TomahawkLabsKB/m3501_stm32f072/Firmware/Locking Switch Logic/Keymap_C_Explanation1.png

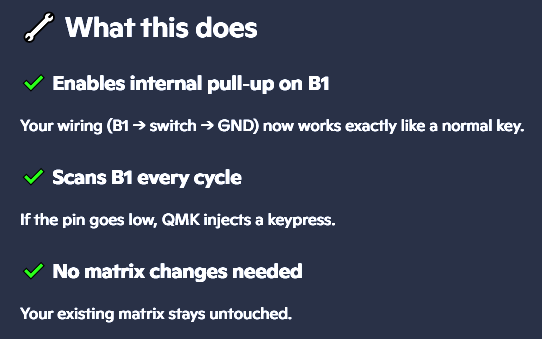
Firmware/Locking Switch Logic/Keymap_C_Explanation1.png
