TomahawkLabsKB/m3501_stm32f072/Firmware/Locking Switch Logic/Keymap_C_Explanation2.png

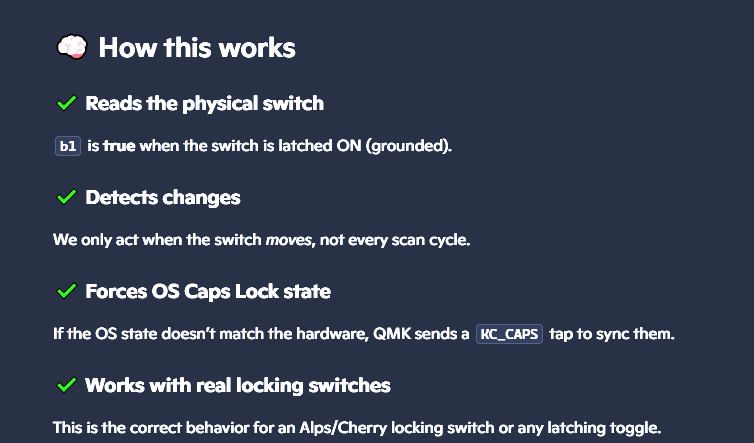
Firmware/Locking Switch Logic/Keymap_C_Explanation2.png
