TomahawkLabsKB/m3501_stm32f072/Images/Cable/Oops.jpeg

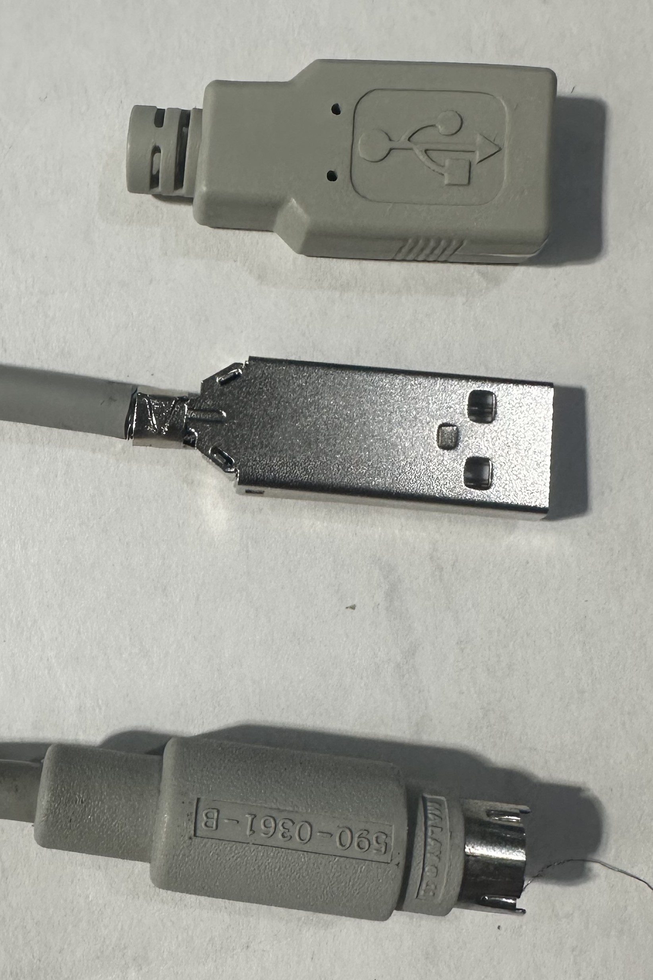
Images/Cable/Oops.jpeg
