TomahawkLabsKB/m3501_stm32f072/Images/Cable/SheathingLength.jpeg

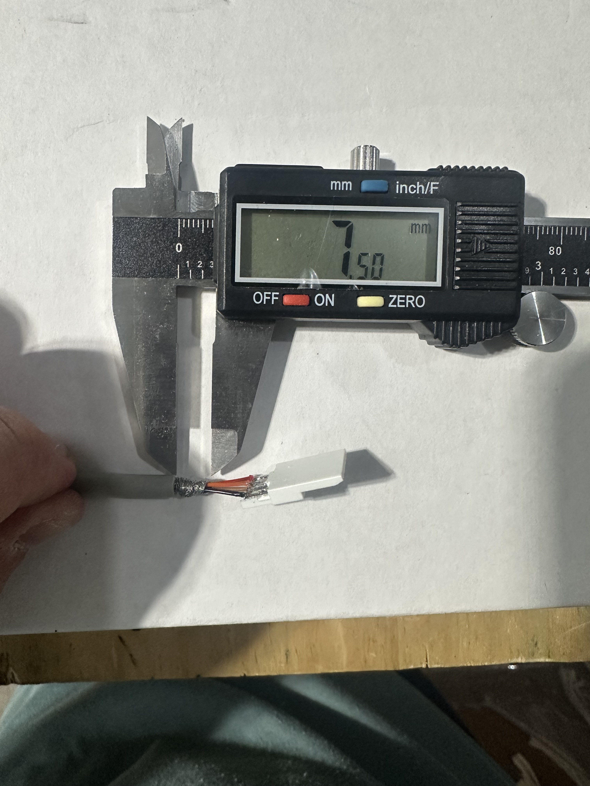
Images/Cable/SheathingLength.jpeg
