TomahawkLabsKB/m3501_stm32f072/Images/Cable/WireLength.jpeg

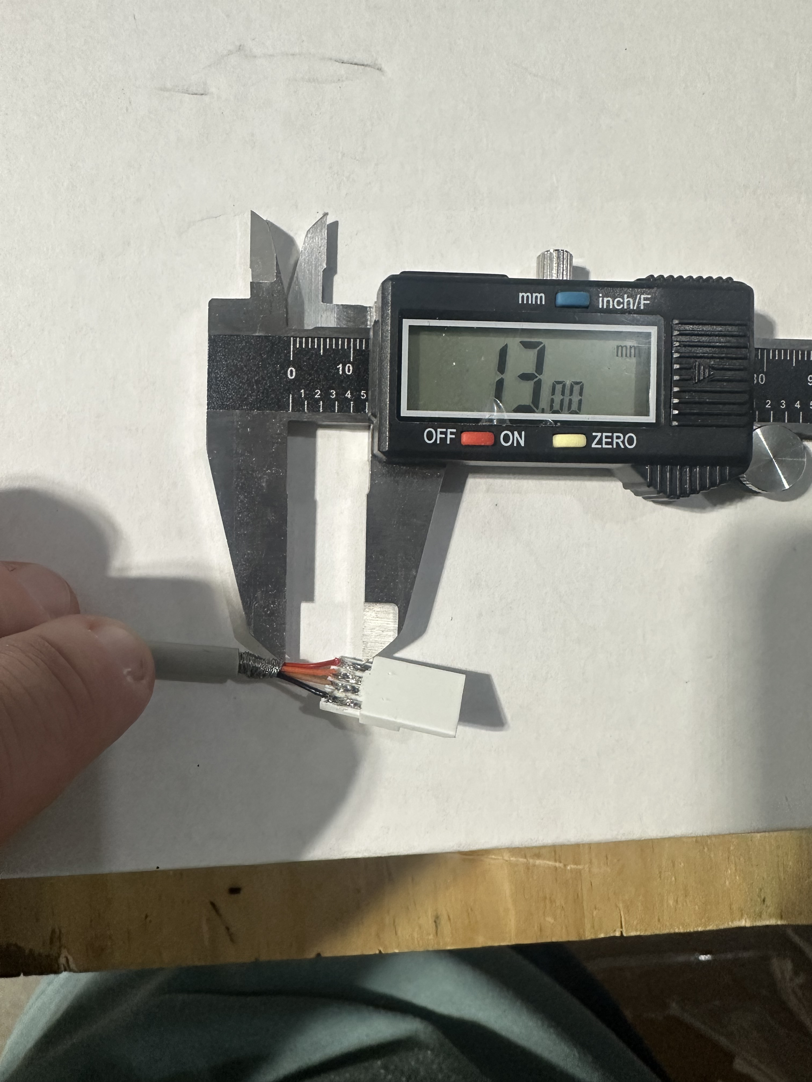
Images/Cable/WireLength.jpeg
