TomahawkLabsKB/m3501_stm32f072/Images/Daughterboard/Daughterboard.jpeg

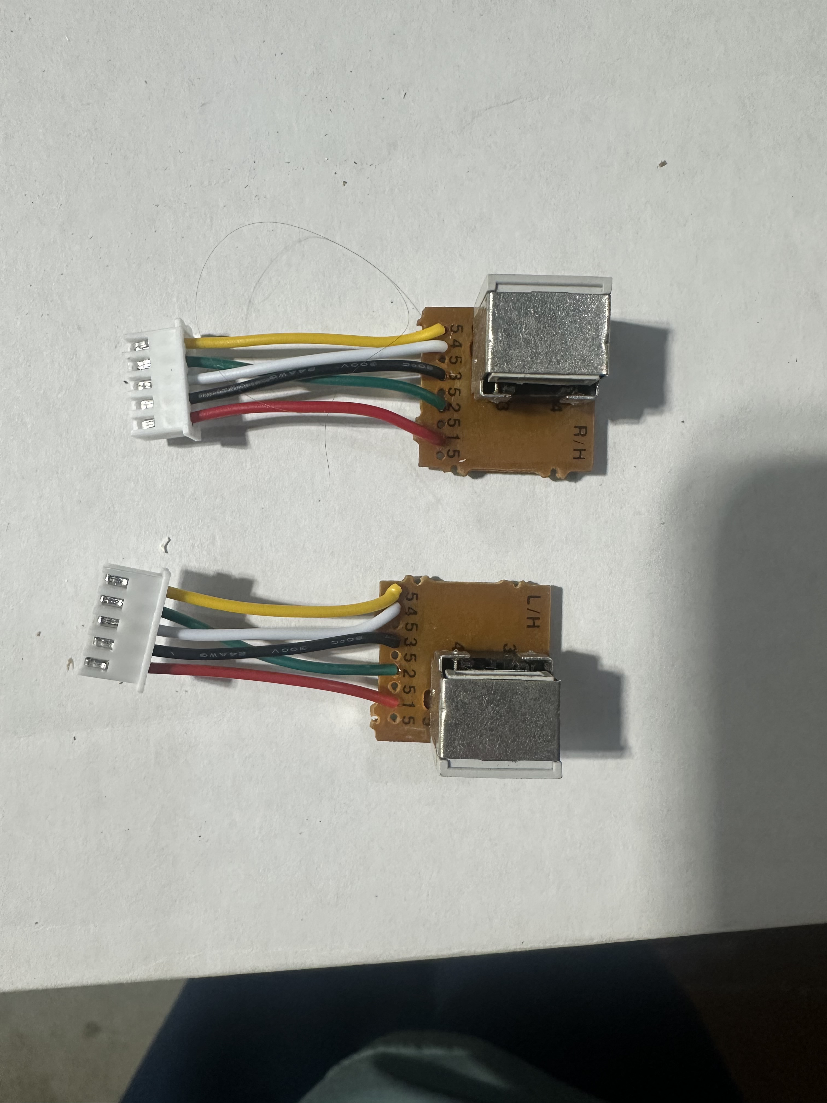
Images/Daughterboard/Daughterboard.jpeg
