TomahawkLabsKB/m3501_stm32f072/Images/Daughterboard/DaughterboardLength.jpeg

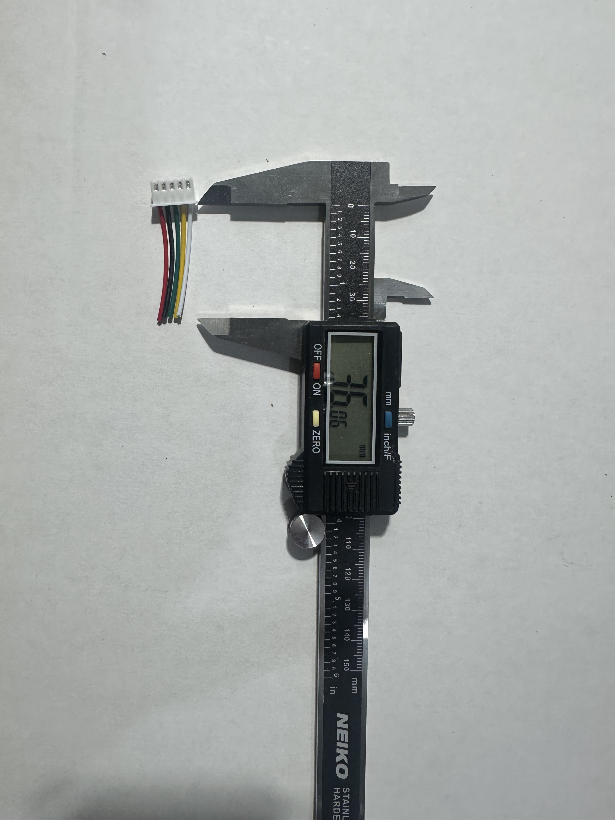
Images/Daughterboard/DaughterboardLength.jpeg
