TomahawkLabsKB/m3501_stm32f072/Images/Daughterboard/LeftDaughterboard.jpeg

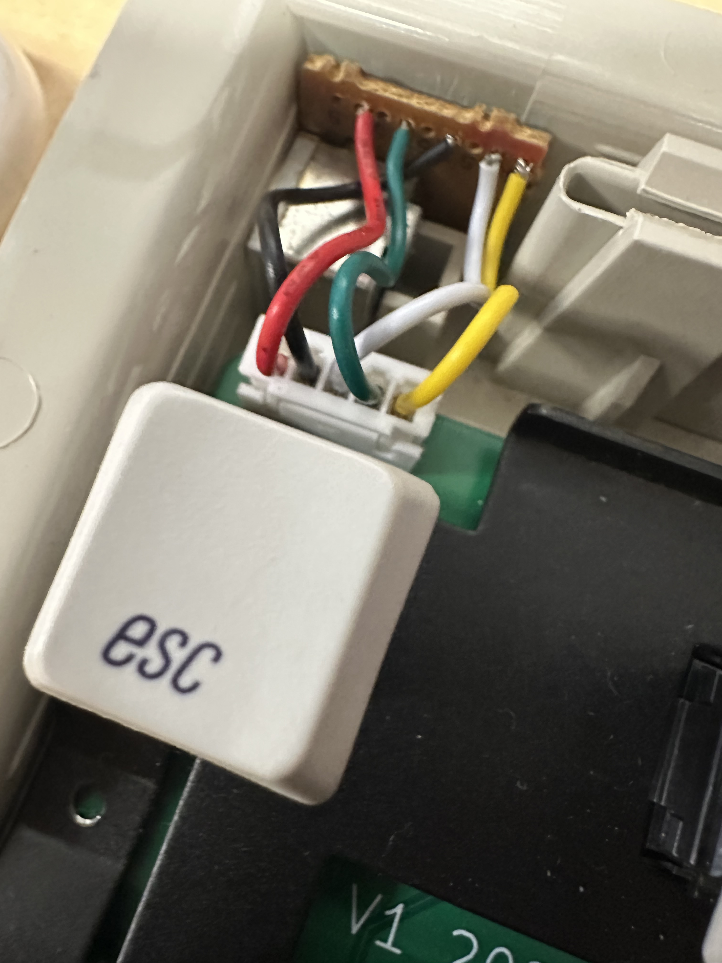
Images/Daughterboard/LeftDaughterboard.jpeg
