TomahawkLabsKB/m3501_stm32f072/Images/Daughterboard/RightDaughterboard.jpeg

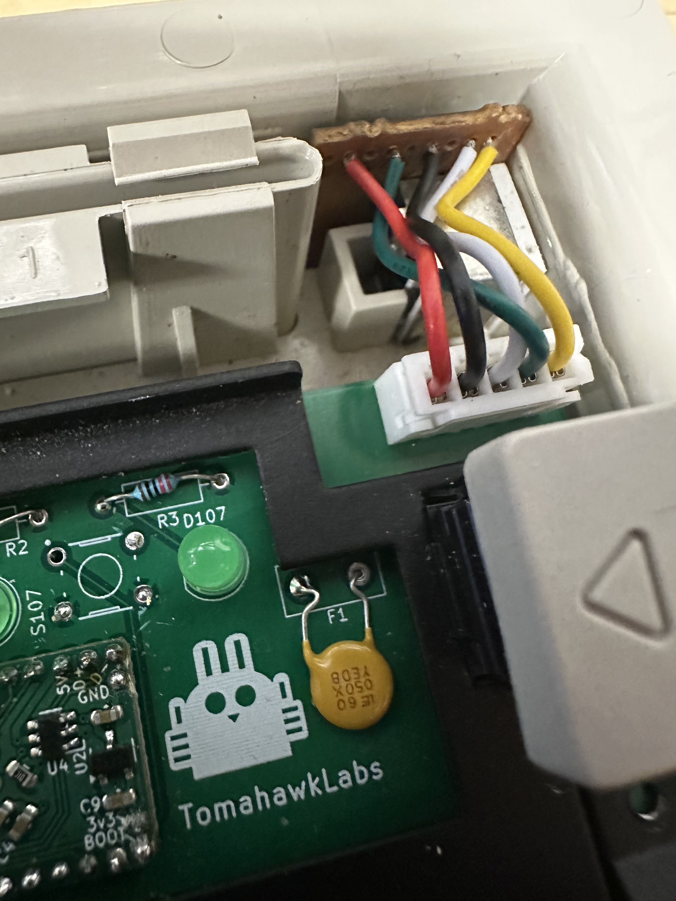
Images/Daughterboard/RightDaughterboard.jpeg
