TomahawkLabsKB/m3501_stm32f072/Images/PCB/Diodes.jpeg

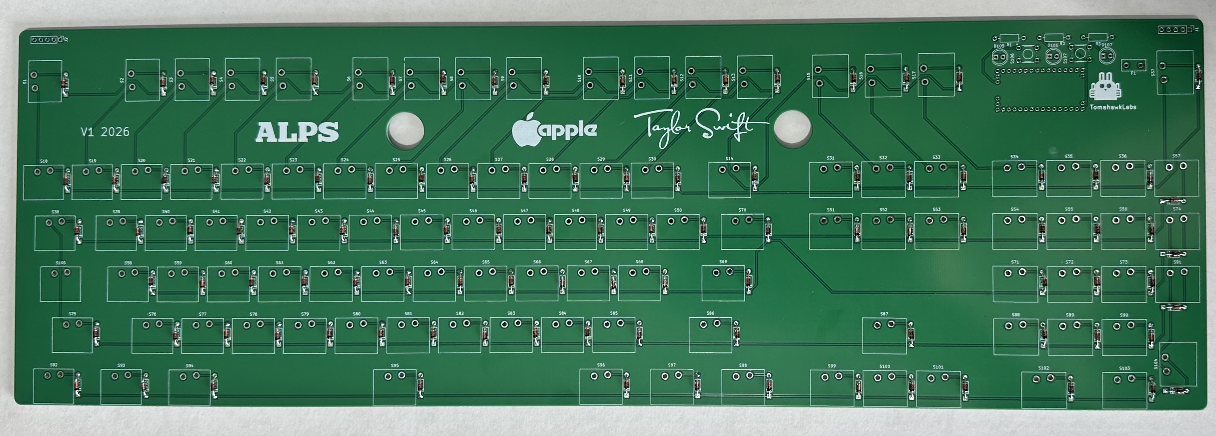
Images/PCB/Diodes.jpeg
