TomahawkLabsKB/m3501_stm32f072/Images/PCB/FullyPopulated.jpeg

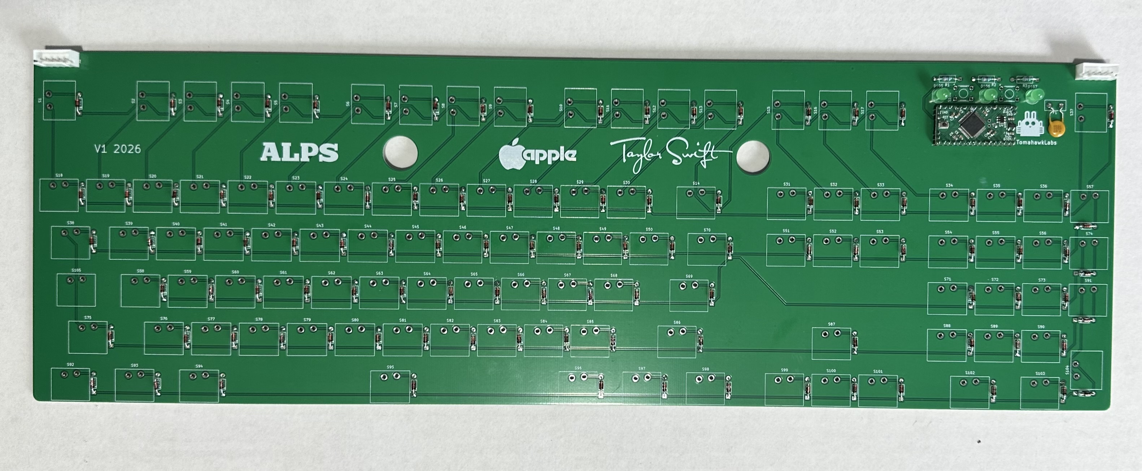
Images/PCB/FullyPopulated.jpeg
