TomahawkLabsKB/m3501_stm32f072/Images/PCB/RearEmpty.jpeg

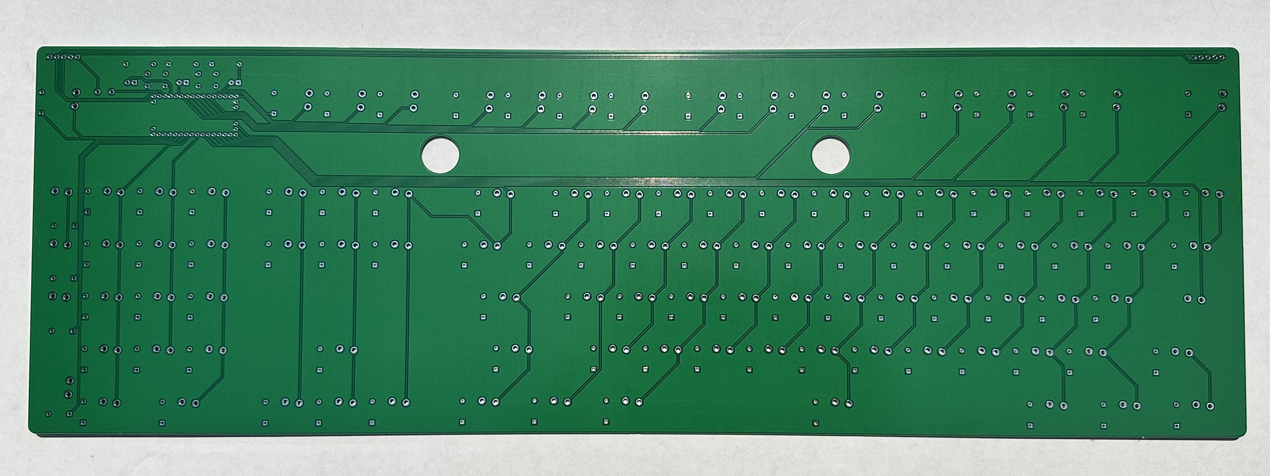
Images/PCB/RearEmpty.jpeg
