TomahawkLabsKB/m3501_stm32f072/Images/Parts Kit/MCU.jpeg

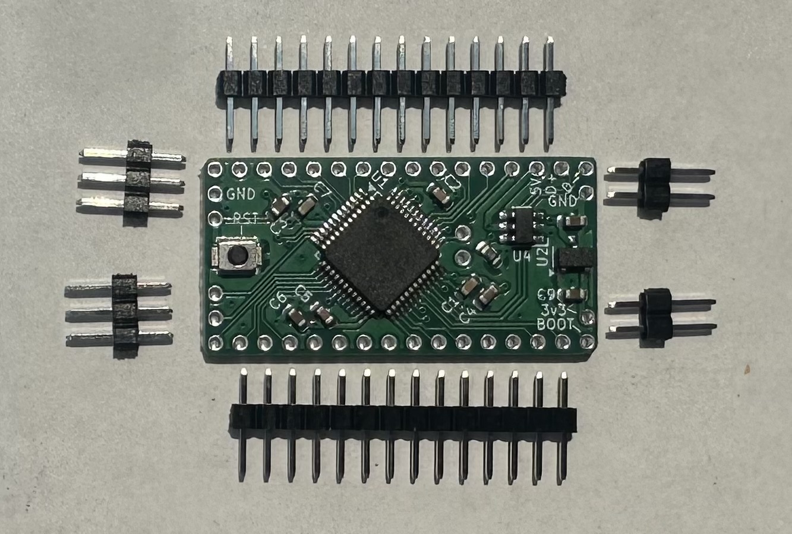
Images/Parts Kit/MCU.jpeg
