TomahawkLabsKB/m3501_stm32f072/Images/Cable/Step01.jpeg

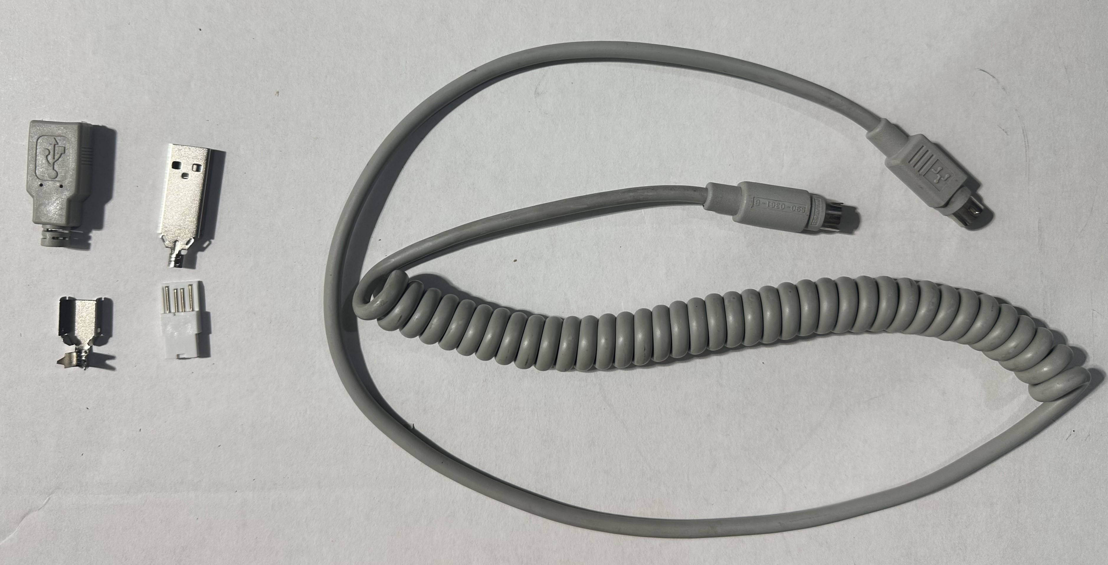
Images/Cable/Step01.jpeg
