TomahawkLabsKB/m3501_stm32f072/Images/Cable/Step02.jpeg

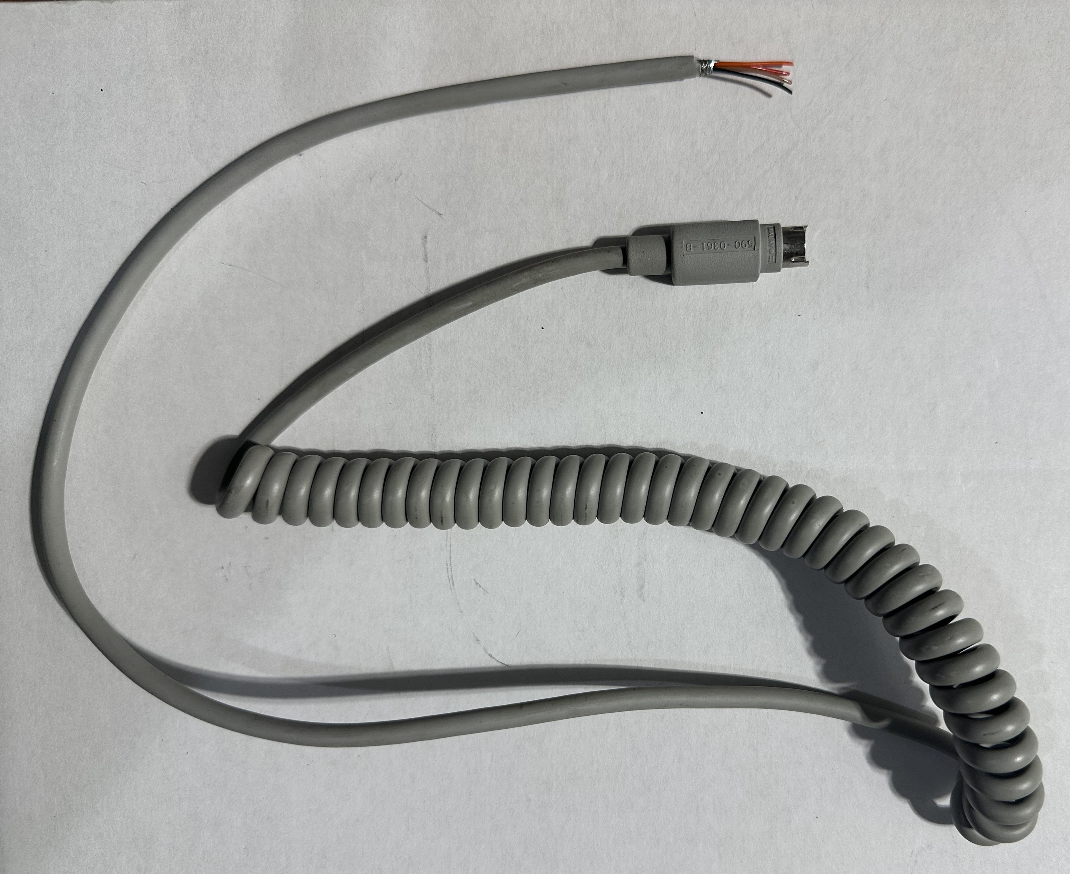
Images/Cable/Step02.jpeg
