TomahawkLabsKB/m3501_stm32f072/Images/Cable/Step03.jpeg

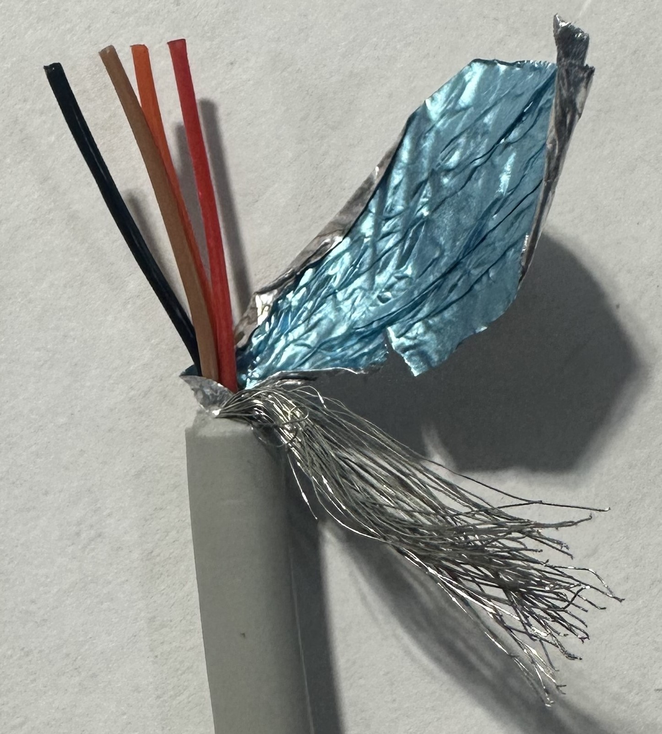
Images/Cable/Step03.jpeg
