TomahawkLabsKB/m3501_stm32f072/Images/Cable/Step05.jpeg

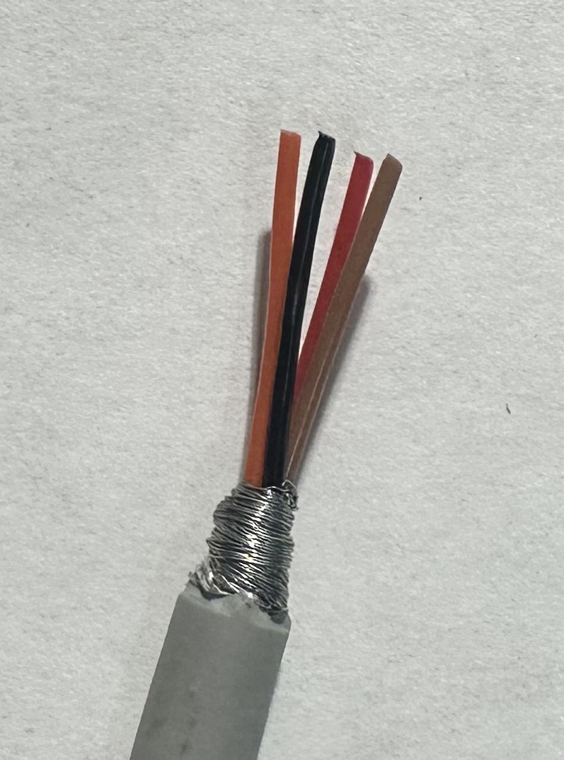
Images/Cable/Step05.jpeg
