TomahawkLabsKB/m3501_stm32f072/Images/Cable/Step06.jpeg

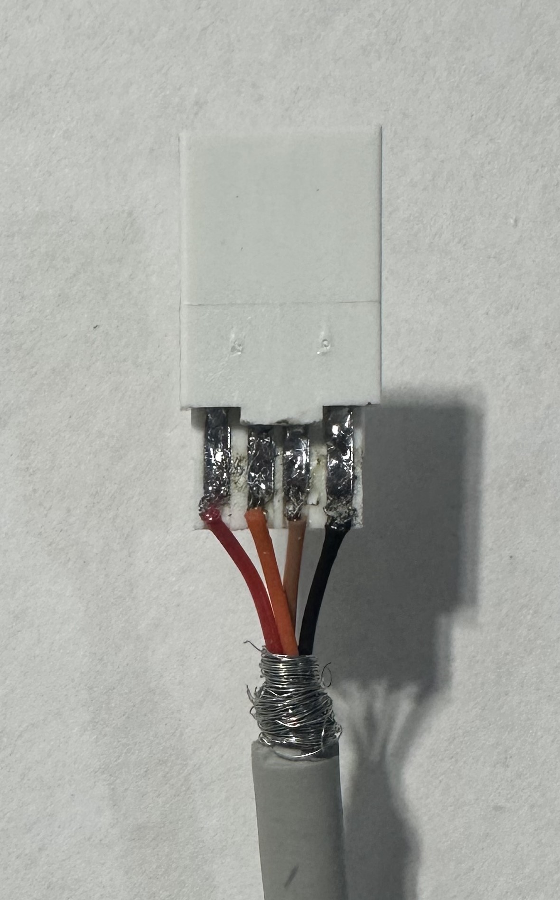
Images/Cable/Step06.jpeg
