TomahawkLabsKB/m3501_stm32f072/Images/Cable/Step07.jpeg

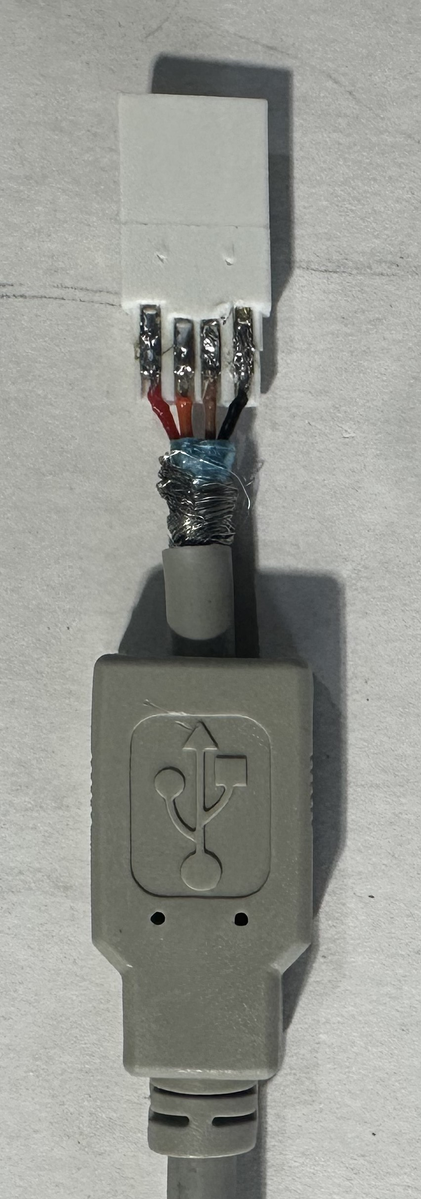
Images/Cable/Step07.jpeg
