TomahawkLabsKB/m3501_stm32f072/Images/Cable/Step08.jpeg

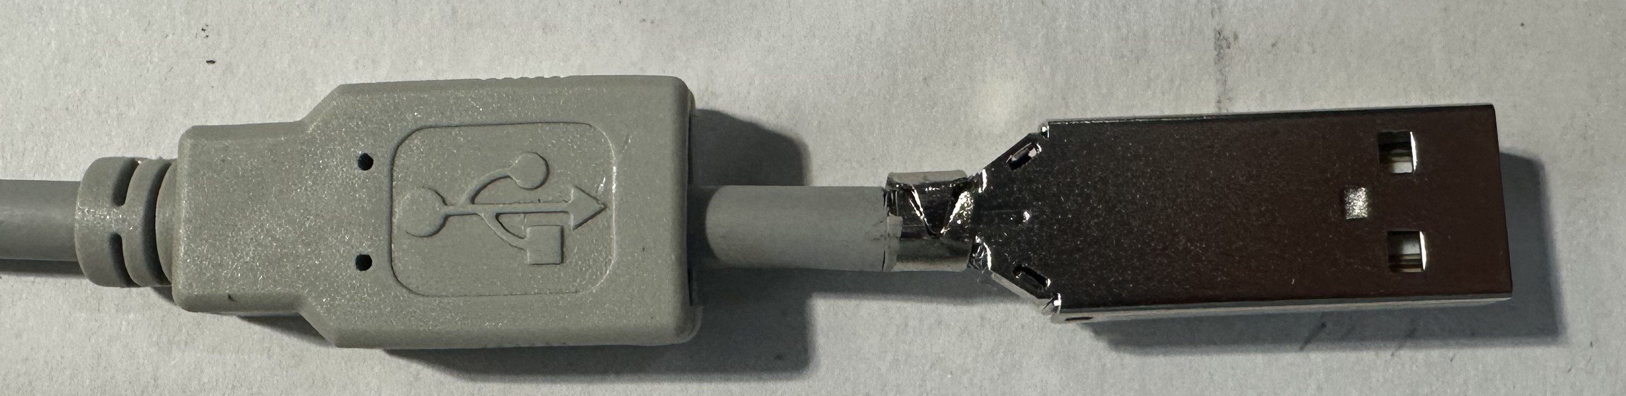
Images/Cable/Step08.jpeg
